daglem/reDIP-CIA/gateware/CIA/cia_interrupt.sv

// ----------------------------------------------------------------------------
// This file is part of reDIP CIA, a MOS 6526/8520/8521 FPGA emulation platform.
// Copyright (C) 2025  Dag Lem <resid@nimrod.no>
//
// This source describes Open Hardware and is licensed under the CERN-OHL-S v2.
//
// You may redistribute and modify this source and make products using it under
// the terms of the CERN-OHL-S v2 (https://ohwr.org/cern_ohl_s_v2.txt).
//
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
// Source location: https://github.com/daglem/reDIP-CIA
// ----------------------------------------------------------------------------

`default_nettype none

module cia_interrupt (
    input  cia::model_t model,
    input  logic[1:0]   icr65,
    input  logic        clk,
    input  logic        phi2_up,
    input  logic        phi2_dn,
    input  logic        res,
    input  logic        rd,
    input  logic        we,
    input  cia::reg4_t  addr,
    /* verilator lint_off UNUSEDSIGNAL */
    input  cia::reg8_t  data,
    /* verilator lint_on UNUSEDSIGNAL */
    input  logic[4:0]   sources,
    output cia::reg8_t  regs,
    output logic        irq_n
    );

    logic [4:0] sources_prev;  // For MOS 8520 delay
    logic [4:0] sources_model;
    logic [4:0] flags;
    logic [4:0] flags_prev;
    logic [4:0] mask;
    logic       r_flags;
    logic       w_mask;
    logic       w_mask_prev;
    logic       ir_clr;
    logic       ir_clr_prev;
    logic       ir_clr_model;
    logic       ir_set;
    logic       ir_set_phi2;  // For MOS 8521 delay
    logic       ir_set_prev;  // For MOS 6526 delay
    logic       ir_set_model;
    cia::reg8_t icr;
/* verilator lint_off UNUSEDSIGNAL */
    cia::reg8_t icr_prev;
/* verilator lint_on UNUSEDSIGNAL */
    logic       icr7;
    logic       icr7_prev;
    logic       irq;
    logic       irq_prev;

    always_comb begin
        r_flags = rd && addr == 'hD;
        w_mask  = we && addr == 'hD;

        sources_model = `MODEL_EQ_MOS8520 ? sources_prev : sources;
        ir_clr_model  = ir_clr;
        ir_clr_model |= (model == cia::MOS6526) ? ir_clr_prev : 1'b0;

        for (int i = 0; i < 5; i++) begin
            // SR latches setting interrupt source flags.
            // Note that in the MOS 6526, ir_clear is held a bit longer than
            // the timer B interrupt signal (ICR bit 1). Timer A interrupt
            // signals (ICR bit 0) are known not to be affected, however it
            // should be investigated whether any of the other bits are.
            if      (sources_model[i])               flags[i] = 1;
            else if (i == 1 ? ir_clr_model : ir_clr) flags[i] = 0;
            else                                     flags[i] = flags_prev[i];
        end

        ir_set = |(flags & mask);
        unique case (model)
          cia::MOS6526: ir_set_model = ir_set_prev;
          cia::NA,
          cia::MOS8521: ir_set_model = ir_set_phi2;
`ifndef NO_MOS8520
          cia::MOS8520: ir_set_model = ir_set;
`endif
        endcase

        // SR/RS latch setting IR flag and /IRQ pad.
        unique case ({ ir_set_model, ir_clr_model })
          2'b00: { icr7, irq } = { icr7_prev, irq_prev };
          2'b01: { icr7, irq } = 2'b00;
          2'b10: { icr7, irq } = 2'b11;
          2'b11: { icr7, irq } = 2'b10;
        endcase

        irq_n = ~irq;
        icr   = { icr7, 2'b0, flags };
        // When ICR bits are cleared by ir_clr, ICR bits set in the previous
        // cycle can still be read out. A possible explanation for this is that
        // polysilicon strips used as gates to drive read bits to 0 have
        // considerable capacitance delay due to their length, and are driven
        // by the positive output of weak inverters.
        regs  = icr;
        regs |= { icr_prev[7], icr65, (model == cia::MOS6526) ? 5'b0 : icr_prev[4:0] };
    end

    always_ff @(posedge clk) begin
        if (phi2_dn) begin
            // Delay interrupt sources for the MOS 8520.
            sources_prev <= sources;
            // Delay setting of ICR bit 7 / IRQ for the MOS 6526.
            ir_set_prev <= ir_set;
            // Keep ICR value for the next cycle for MOS 8521 and MOS 8520.
            icr_prev <= icr;
        end

        // Update latch states.
        icr7_prev  <= icr7;
        irq_prev   <= irq;
        flags_prev <= flags;

        // Delay ir_clr a bit for the MOS 6526. ir_clr is driven to 0 later
        // than ir_set at the rising edge of PHI1. This implies that when
        // ir_set and ir_clr are both high at PHI2, and both are driven to 0
        // at the rising edge of PHI1, the interrupt SR latch will be reset.
        ir_clr_prev <= ir_clr;

        if (phi2_up | w_mask) begin  // Has the same effect as "if (phi2)"
            ir_set_phi2 <= ir_set;
        end

        if (`MODEL_EQ_MOS8520 && phi2_up) begin
            ir_clr <= 0;
        end else if (phi2_dn) begin
            ir_clr <= r_flags | res;
        end

        // Normally, a write to the ICR takes effect at PHI1.
        // An interesting observation is that if the ICR is written in two
        // consecutive cycles, the second write takes effect already at PHI2.
        // The 650x/651x MPUs sample interrupt signals on PHI2, so we must
        // implement this behavior accurately.
        if (res) begin
            mask <= '0;
        end else if (w_mask && (phi2_dn || w_mask_prev)) begin
            mask <= data[7] ? mask | data[4:0] : mask & ~data[4:0];
        end

        if (phi2_dn) begin
            w_mask_prev <= w_mask;
        end
    end
endmodule
